shangathechild/kyber/screenshots/pcb1.png

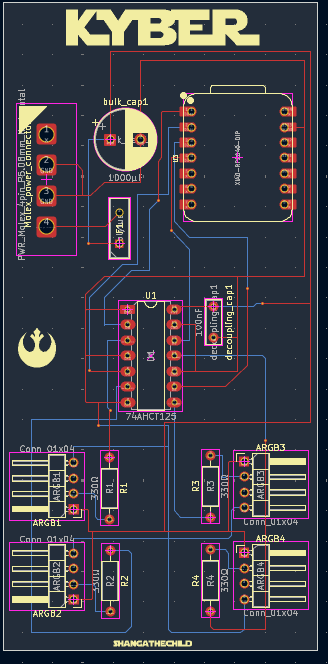
screenshots/pcb1.png
